petorikooru/Malkuth/main/malkuth_audio.h

#define USE_EXPERIMENTAL 1

#include <AudioTools.h>
#include <AudioTools/Disk/AudioSourceSDFAT.h>
#include <AudioTools/AudioCodecs/CodecFLACFoxen.h>
#include <AudioTools/AudioCodecs/CodecMP3Helix.h>
#include <AudioTools/AudioCodecs/CodecAACHelix.h>
#include <AudioTools/AudioCodecs/CodecWAV.h>
#include <AudioTools/Concurrency/RTOS.h>
#include "AudioTools/AudioLibs/Concurrency.h" 

#include <SdFat.h>

#include "malkuth_helper.h"

typedef struct {
    String artist;
    String title;
    String album;

    float duration;    
    uint64_t total_samples;
    uint32_t sample_rate;
    uint32_t data_offset;
} AudioMetadata;

class CustomI2S : public I2SStream {
public:
  uint64_t bytes_written = 0;

  size_t write(const uint8_t* buffer, size_t size) override {
    size_t res      = I2SStream::write(buffer, size);
    bytes_written  += res;

    return res;
  }
  float getAudioCurrentTime() {
    auto info = audioInfo();

    if (info.sample_rate == 0) return 0.0f;

    int byte_rate = info.sample_rate * info.channels * (info.bits_per_sample / 8);
    
    return byte_rate > 0 ? (float)bytes_written / byte_rate : 0.0f;
  }

  void resetBytesWritten() {
    bytes_written = 0;
  }
};

// MP3 duration estimation
static const int sampleRateTable[4][3] = {
    {11025,12000,8000},    // MPEG 2.5
    {0,0,0},               // reserved
    {22050,24000,16000},   // MPEG 2
    {44100,48000,32000}    // MPEG 1
};

static const int bitrateTable[2][16] = {
    // MPEG1 Layer III
    {0,32,40,48,56,64,80,96,112,128,160,192,224,256,320,0},
    // MPEG2/2.5 Layer III
    {0,8,16,24,32,40,48,56,64,80,96,112,128,144,160,0}
};

class MalkuthAudio {
private:
    FsFile          _audio_file;
    SdFs*           _sd;
    bool            _playing                = false;
    uint8_t         _volume                 = 10;
    static float    _current_duration;
    char            _current_audiopath[255] = {};

    uint32_t data_start = 0;

    AudioSourceVector<FsFile>*  _source;
    AudioPlayer*                _player;

    // TODO :  Multiprocessing on Audio
    // BufferRTOS<uint8_t>  _buffer_audio;
    // QueueStream<uint8_t> _queue_audio;
    // StreamCopy*          _copier; 

    CustomI2S _i2s;

    MultiDecoder      _decoder;
    FLACDecoderFoxen  _decoder_flac;
    MP3DecoderHelix   _decoder_mp3;
    WAVDecoder        _decoder_wav;

    AudioMetadata  _current_track;

    bool _please_update = false;
    bool _not_a_music   = false;

    static MalkuthAudio* self;

    enum class CoverPriority {
        NONE = 0,
        COVER_PNG   = 1,
        COVER_JPG   = 2,
        SMALL_COVER = 3
    };
    CoverPriority _cover_priority = CoverPriority::NONE;
    char      _cover_path[128] = {};
    ImageType _image_type;

    static FsFile*  file_to_stream_cb(const char* path, FsFile& old_file);
    FsFile*         file_to_stream(const char* path, FsFile& old_file);

    static void  metadata_print_cb(MetaDataType type, const char* str, int len);
    void         metadata_print(MetaDataType type, const char* str, int len);

    static AudioMetadata get_metadata(FsFile& file, const char* path);

    static AudioMetadata get_metadata_flac(FsFile& file);
    static AudioMetadata get_metadata_flac_vorbis(FsFile& file, uint32_t size);

    static AudioMetadata get_metadata_mp3(FsFile& file);
    static AudioMetadata get_metadata_mp3v1(FsFile& file);
    static float         get_metadata_mp3_duration(FsFile& file);

    static bool  mp3_id3skip(FsFile& file);
    static bool  mp3_frameheader(FsFile& file, uint32_t& hdr);
    static int   mp3_sampleframe(uint32_t hdr);
    static int   mp3_samplerate(uint32_t hdr);
    static int   mp3_bitrate(uint32_t hdr);
    static int   mp3_xing_offset(uint32_t hdr);

    static AudioMetadata get_metadata_wav(FsFile& file);

public:
  // MalkuthAudio():
  //   _buffer_audio(1024 * 10),
  //   _queue_audio(_buffer_audio)
  // {}

    bool init(uint8_t pin_bck = 8, uint8_t pin_ws = 17, uint8_t pin_data = 18);
    void reset();
  
    AudioMetadata get_metadata();

    void process_directory(const char* path);
    void process_albumcover(String path);

    void set_sdfs(SdFs& sd);
    void set_volume(uint8_t percent);
    void set_path(const char* path);
    void set_index(int16_t index);
    void set_position(uint8_t percent);

    size_t loop();
    size_t loop_all();
    void   start_loop();

    void next();
    void previous();

    void toggle();
    void toggle(bool active);

    uint8_t get_volume();
    bool    get_update();
    bool    get_status();
    float   get_position();
    char*   get_coverpath();
    char*   get_audiopath();
    ImageType get_covertype();
    char*   get_file_extension();

    bool    is_actually_audio();
    void  yeah_i_have_updated();

};
